nppc/Heater12VControl/Images/90pFinished1.jpg

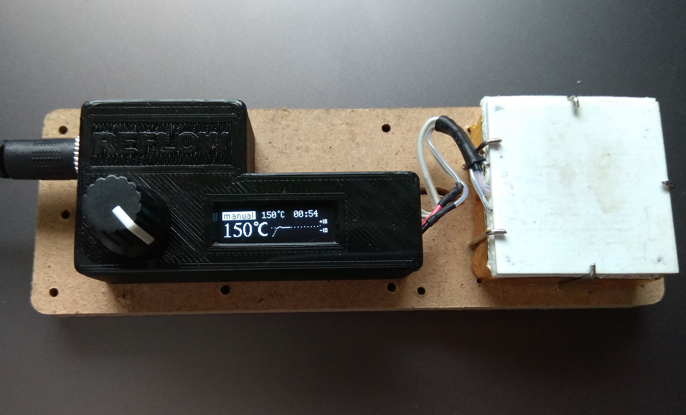
Images/90pFinished1.jpg
