nppc/Heater12VControl/Images/HeatingPlate1.jpg

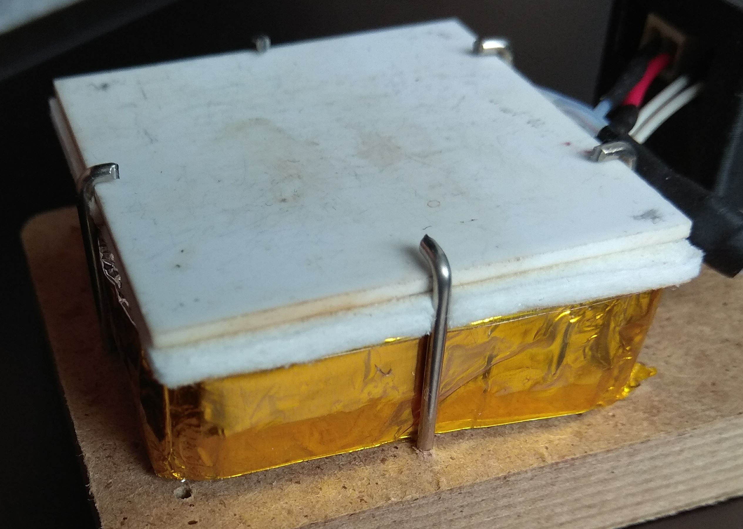
Images/HeatingPlate1.jpg
