nppc/Heater12VControl/Images/HeatingPlate.jpg

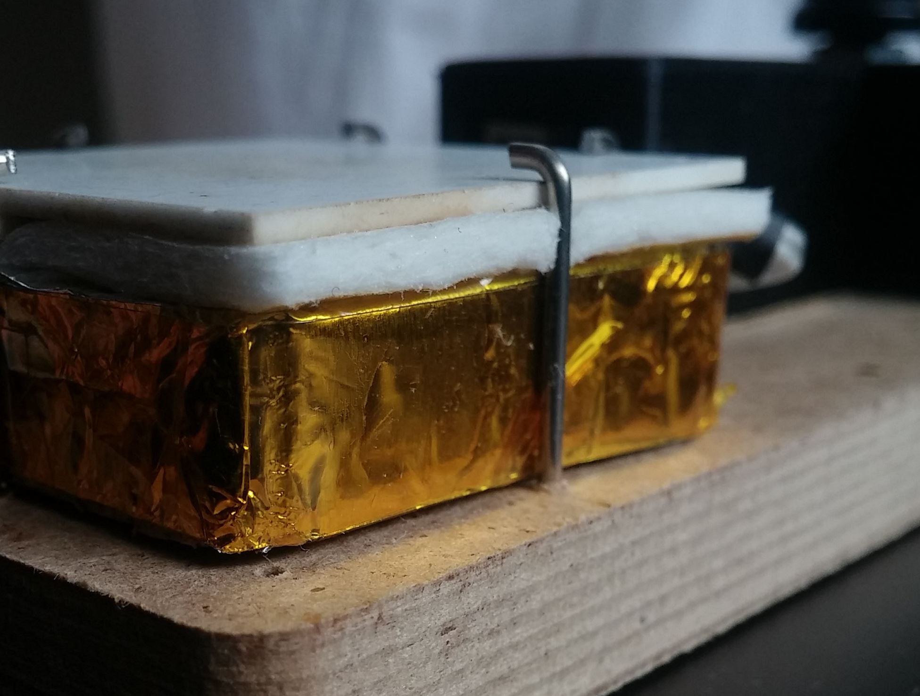
Images/HeatingPlate.jpg
