nppc/Heater12VControl/Images/HeatingPlateInsulation.jpg

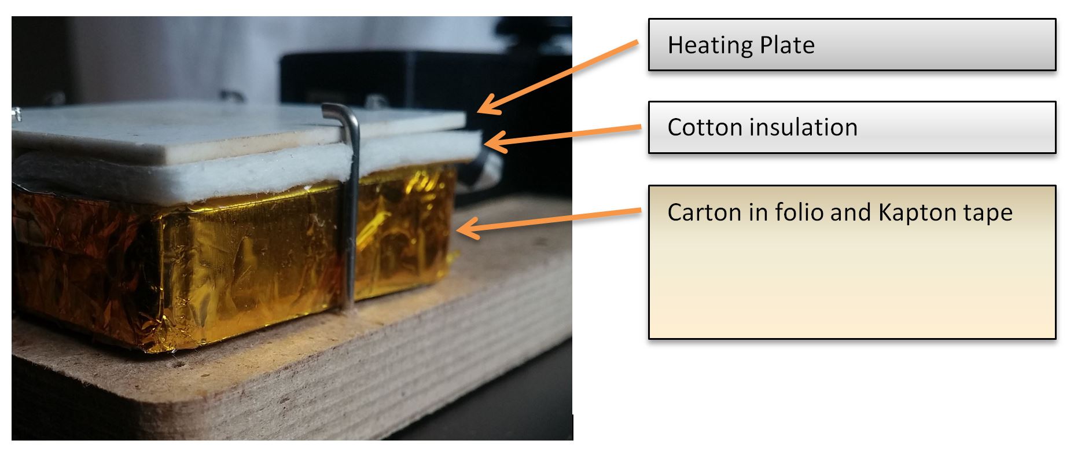
Images/HeatingPlateInsulation.jpg
