nppc/Heater12VControl/Images/OLEDPrototype.png

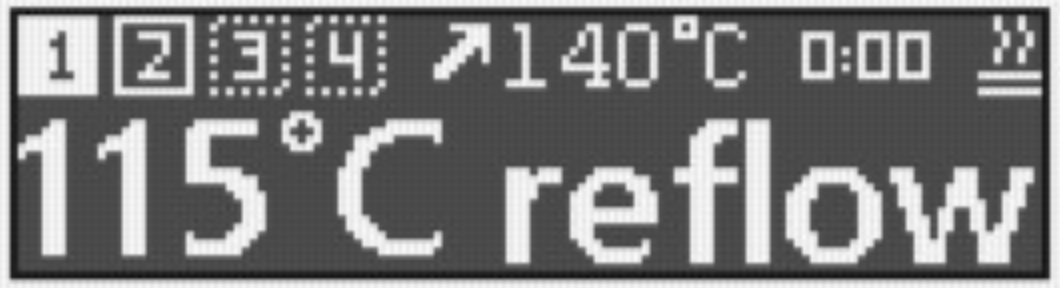
Images/OLEDPrototype.png
