nppc/Heater12VControl/Images/ReflowPlate_Connections.jpg

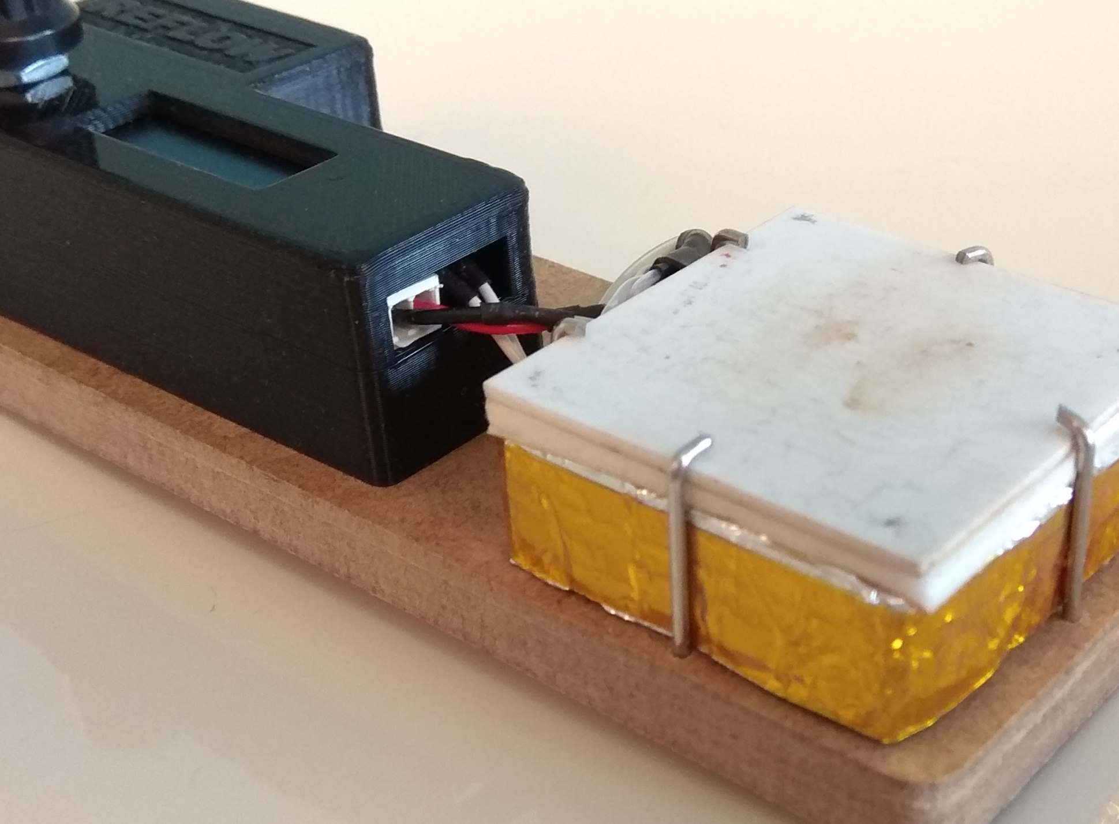
Images/ReflowPlate_Connections.jpg
