nppc/Heater12VControl/Images/ReflowPlate_Power_USB.jpg

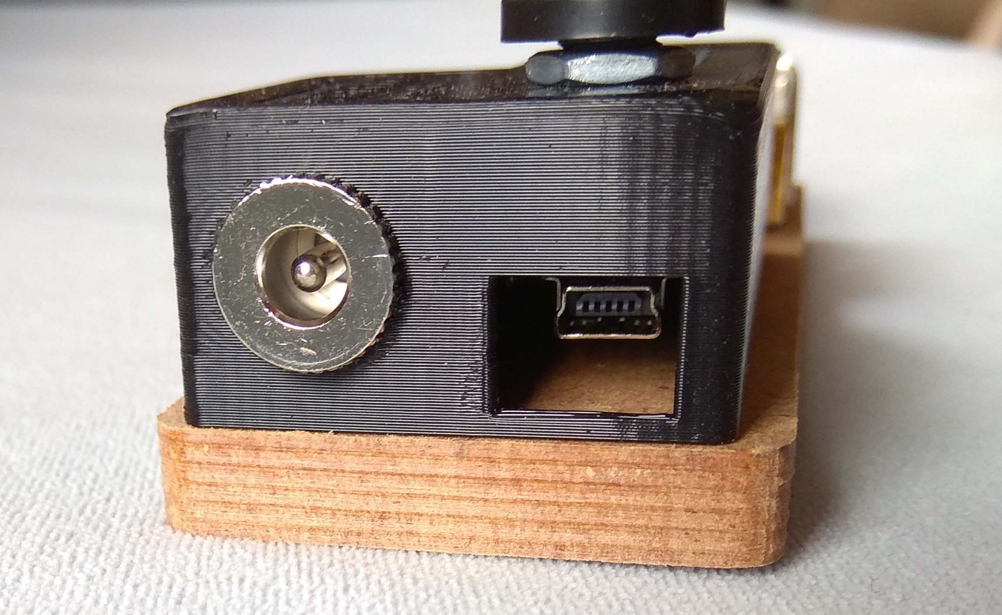
Images/ReflowPlate_Power_USB.jpg
