nppc/Heater12VControl/Arduino/HeaterControlV2/oled.ino

#ifdef OLED
//8X10
static const uint8_t u8g_clear_bits[] U8X8_PROGMEM = {
	0b00000000,
	0b00000000,
	0b00000000,
	0b00000000,
	0b00000000,
	0b00000000,
	0b00000000,
	0b00000000,
	0b00000000,
	0b00000000
};
//8X10
static const uint8_t u8g_heating_bits[] U8X8_PROGMEM = {
	0b01001000,
	0b00100100,
	0b00100100,
	0b01001000,
	0b10010000,
	0b10010000,
	0b01001000,
	0b00100100,
	0b00000000,
	0b11111110
};

//40x10 (manual)
static const uint8_t u8g_manual_bits[] U8X8_PROGMEM = {
  0xFF, 0xFF, 0xFF, 0xFF, 0xFF, 0xFF, 0xFF, 0xFF, 0xFF, 0xEF, 0xFF, 0xFF, 
  0xFF, 0xFF, 0xEF, 0x03, 0x8E, 0xE3, 0x36, 0xEE, 0xDB, 0x7E, 0xDB, 0xF6, 
  0xED, 0xDB, 0x0E, 0xDB, 0x36, 0xEC, 0xDB, 0x76, 0xDB, 0xD6, 0xED, 0xDB, 
  0x76, 0xDB, 0xD6, 0xED, 0xDB, 0x0E, 0xDB, 0x30, 0xEC, 0xFF, 0xFF, 0xFF, 
  0xFF, 0xFF
};

// 8X9 (Celsius)
static const uint8_t u8g_celsius_bits[] U8X8_PROGMEM = {
	0b00000010,
	0b01100101,
	0b10010010,
	0b00010000,
	0b00010000,
	0b00010000,
	0b00010000,
	0b10010000,
	0b01100000
};

//16X18
static const uint8_t u8g_bigCelsius_bits[] U8X8_PROGMEM = {
	0b00001110,0b00000000,
	0b00011011,0b01111000,
	0b00010001,0b11111110,
	0b10011011,0b10001111,
	0b10001110,0b00000011,
	0b11000000,0b00000001,
	0b11000000,0b00000001,
	0b11100000,0b00000000,
	0b11100000,0b00000000,
	0b11100000,0b00000000,
	0b11100000,0b00000000,
	0b11100000,0b00000000,
	0b11100000,0b00000000,
	0b11000000,0b00000001,
	0b11000000,0b00000011,
	0b10000000,0b10000111,
	0b00000000,0b11111111,
	0b00000000,0b01111100
};

//10X10
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
	u8g2.drawXBMP(3, 5, 8, 9, u8g_celsius_bits);
	uint16_t curval=(int)currentTemp;
	uint16_t tmpcoord = (curval<100 ? 3 : 0);	// two or three digits number
	u8g2.setCursor(tmpcoord, 27);
	u8g2.setFont(u8g2_font_profont12_tn);	//numeric font for preset temperature and timer
	u8g2.print(curval);

	if(sel==1){
		u8g2.drawRBox(0+22,4,51,25,4);
		u8g2.drawRFrame(55+22,4,51,25,4);
	}else{
		u8g2.drawRFrame(0+22,4,51,25,4);
		u8g2.drawRBox(55+22,4,51,25,4);
	}
	u8g2.setDrawColor(2);	// restore default mode
	u8g2.setFont(u8g2_font_t0_22_mf);
	u8g2.drawStr(3+22,24,"Auto");
	u8g2.drawStr(59+22,24,"Man.");
	u8g2.sendBuffer();
}

// this routine is a part of other routine, so no sendBuffer...
void printManual(){
	u8g2.drawXBMP( 0, 0, 40, 10, u8g_manual_bits);
}

// this routine is a part of other routine, so no sendBuffer...	
void printPresetTemperature(){
	u8g2.setFont(u8g2_font_profont12_tn);	//numeric font for preset temperature and timer
	//u8g2.setFontMode(1);
	u8g2.setCursor(48, 9);
	uint16_t curval=(int)setPoint;
	u8g2.print(curval);
	uint16_t tmpcoord = 49+6*(curval<100 ? 2 : 3);	// two or three digits number
	u8g2.setBitmapMode(1);
	u8g2.drawXBMP(tmpcoord, 0, 8, 9, u8g_celsius_bits);
}

// this routine is a part of other routine, so no sendBuffer...	
// mm:ss
void printTime(uint16_t t) {
	//u8g2.setFontMode(1);
	u8g2.setCursor(87, 9);
	t = t % 3600;	// cut off hours
	uint8_t m = t / 60;
	uint8_t s = t % 60;
	printNumber00(m);
	u8g2.print(':');
	printNumber00(s);
}
// this routine is a part of other routine, so no sendBuffer...	
void printNumber00(uint8_t n) {
	if (n<10) {u8g2.print('0');}
	u8g2.print(n);
}

void printHeaterState(){
	if(digitalRead(MOSFET_PIN)){
		u8g2.drawXBMP( 120, 0, 8, 10, u8g_heating_bits);
	}else{
		u8g2.drawXBMP( 120, 0, 8, 10, u8g_clear_bits);
	}
}

// this routine is a part of other routine, so no sendBuffer...	
void printCurrentTemperature(){
	u8g2.setFont(u8g2_font_timR18_tn);	//numeric font for current temperature
	u8g2.setCursor(0, 31);
	uint16_t curval=round(currentTemp);
	u8g2.print(curval);
	uint16_t tmpcoord = 12*(curval<100 ? 2 : 3)+2;	// two or three digits number
	u8g2.drawXBMP(tmpcoord, 13, 16, 18, u8g_bigCelsius_bits);
}

void printAuto(){
	for(uint8_t i=0;i<3;i++){
		uint8_t curtype=0;
		switch (i) {
			case 0:	// Preheat
				if(ControlType==1){curtype=1;}else{curtype=2;}
				break;
			case 1:	// reflow
				if(ControlType==3){curtype=1;}else if(ControlType>3){curtype=2;}
				break;
			case 2:	// cool down
				if(ControlType==5){curtype=1;}else if(ControlType>5){curtype=2;}
		}
		printAutoStateBox(i*12,0,i,curtype); // x,y,step,type
	}
}

void printAutoStateBox(uint8_t x, uint8_t y, uint8_t step, uint8_t type){
// three types of boxes
// 0 - dotted box
// 1 - solid line box
// 2 - filled box
	switch (type) {
		case 0:
			u8g2.drawXBMP(x, y, 10, 10, u8g_autoStepNotActive_bits);
			break;
		case 1:
			u8g2.drawFrame(x, y, 10,10);
			break;
		case 2:
			u8g2.drawBox(x, y, 10,10);
	}
	// print step number (range: 0-2)
	u8g2.setFont(u8g2_font_5x7_tn);	//numeric font for step numbers
	//u8g2.setFontMode(1);
	u8g2.setCursor(x+3,y+8);
	u8g2.print(step+1);
	
	
}
	

void printStepTextGraphic(){
	switch (ControlType) {
		case 1:	// ramp to preheat temperature
			u8g2.drawXBMP(127-59, 31-12, 59, 12, u8g_warm_txt_bits);
			break;
		case 2:	// wait for timer
			u8g2.drawXBMP(127-49, 31-17, 49, 17, u8g_soak_txt_bits);
			break;
		case 3:	// ramp to reflow temperature
			u8g2.drawXBMP(127-59, 31-12, 59, 12, u8g_warm_txt_bits);
			break;
		case 4:	// wait for timer
			u8g2.drawXBMP(127-66, 31-18, 66, 18, u8g_reflow_txt_bits);
			break;
		case 5:	// wait for cooling down
			u8g2.drawXBMP(127-43, 31-18, 43, 18, u8g_cool_txt_bits);
	}	

}
	
#endif
